Home-Sweet-Home-Assistant/Comms-Badge-Voice-Assistant/Hardware/KiCad Project/v0.1.1/Antenna.kicad_sch

## KiCad design Hardware/KiCad Project/v0.1.1/Antenna.kicad_sch (2024-03-10)

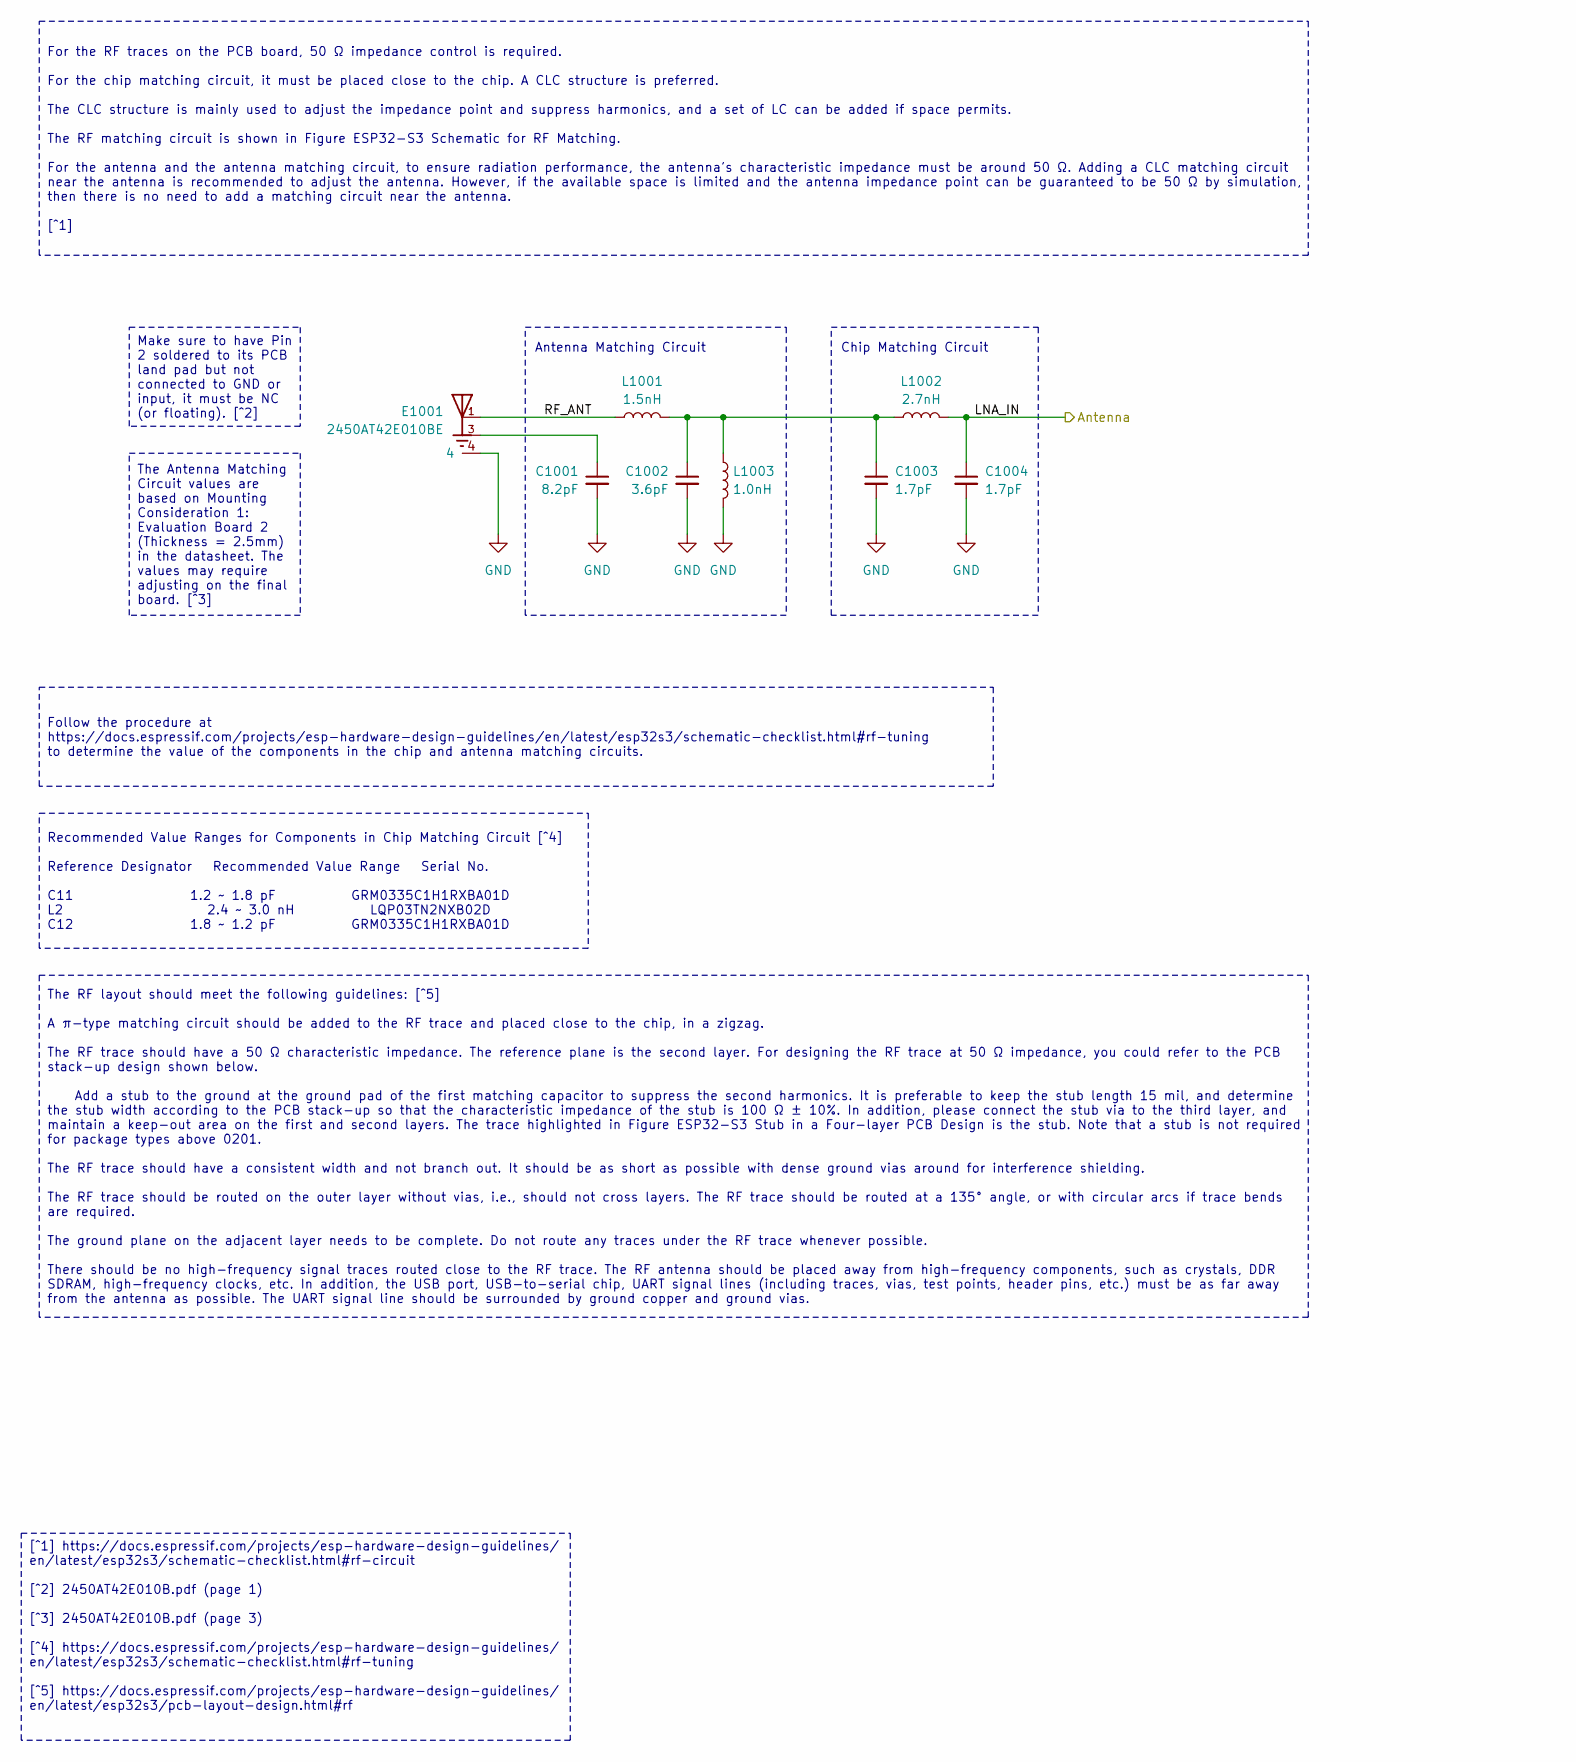
[picture p19: schematic Antenna.kicad_sch]

Parts:
C1001: 8.2pF; C_0402_1005Metric; Mfr. Part # GRM1555C1H8R2CA01D; LCSC # C76984
C1002: 3.6pF; C_0402_1005Metric; Mfr. Part # GRM1555C1H3R6CA01D; LCSC # C913745
C1003, C1004: 1.7pF; C_0402_1005Metric; Mfr. Part # GJM1555C1H1R7BB01D; LCSC # C161313
E1001: 2450AT42E010BE; XDCR_2450AT42E010BE; Mfr. Part # 2450AT42E010B001E; LCSC # C17243480
L1001: 1.5nH; L_0402_1005Metric_Pad0.77x0.64mm_HandSolder; Mfr. Part # LQG15HN1N5B02D; LCSC # C3911113
L1002: 2.7nH; L_0402_1005Metric_Pad0.77x0.64mm_HandSolder; Mfr. Part # LQG15HS2N7B02D; LCSC # C162541
L1003: 1.0nH; L_0402_1005Metric_Pad0.77x0.64mm_HandSolder; Mfr. Part # LQG15HS1N0B02D; LCSC # C162538

Connections:
Antenna: C1004.1, L1002.2
GND: C1001.2, C1002.2, C1003.2, C1004.2, E1001.4, L1003.2
unnamed: C1001.1, E1001.3
unnamed: C1002.1, C1003.1, L1001.2, L1002.1, L1003.1
RF_ANT: E1001.1, L1001.1

Notes on the sheet:
The RF layout should meet the following guidelines: [^5] A π-type matching circuit should be added to the RF trace and placed close to the chip, in a zigzag. The RF trace should have a 50 Ω characteristic impedance. The reference plane is the second layer. For designing the RF trace at 50 Ω impedan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
Recommended Value Ranges for Components in Chip Matching Circuit [^4] Reference Designator Recommended Value Range Serial No. C11 1.2 ~ 1.8 pF GRM0335C1H1RXBA01D L2 2.4 ~ 3.0 nH LQP03TN2NXB02D C12 1.8 ~ 1.2 pF GRM0335C1H1RXBA01D
Follow the procedure at https://docs.espressif.com/projects/esp-hardware-design-guidelines/en/latest/esp32s3/schematic-checklist.html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 to determine the value of the components in the chip and antenna matching circuits.
Make sure to have Pin 2 soldered to its PCB land pad but not connected to GND or input, it must be NC (or floating). [^2]
[^1] https://docs.espressif.com/projects/esp-hardware-design-guidelines/ en/latest/esp32s3/schematic-checklist.html#rf-circuit [^2] 2450AT42E010B.pdf (page 1) [^3] 2450AT42E010B.pdf (page 3) [^4] https://docs.espressif.com/projects/esp-hardware-design-guidelines/ en/latest/esp32s3/schematic-checkli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
The Antenna Matching Circuit values are based on Mounting Consideration 1: Evaluation Board 2 (Thickness = 2.5mm) in the datasheet. The values may require adjusting on the final board. [^3]
For the RF traces on the PCB board, 50 Ω impedance control is required. For the chip matching circuit, it must be placed close to the chip. A CLC structure is preferred. The CLC structure is mainly used to adjust the impedance point and suppress harmonics, and a set of LC can be added if space perm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
Chip Matching Circuit
Antenna Matching Circuit
