Home-Sweet-Home-Assistant/Comms-Badge-Voice-Assistant/Hardware/KiCad Project/v0.1.1/Charging_Battery_Protection.kicad_sch

## KiCad design Hardware/KiCad Project/v0.1.1/Charging_Battery_Protection.kicad_sch (2024-03-10)

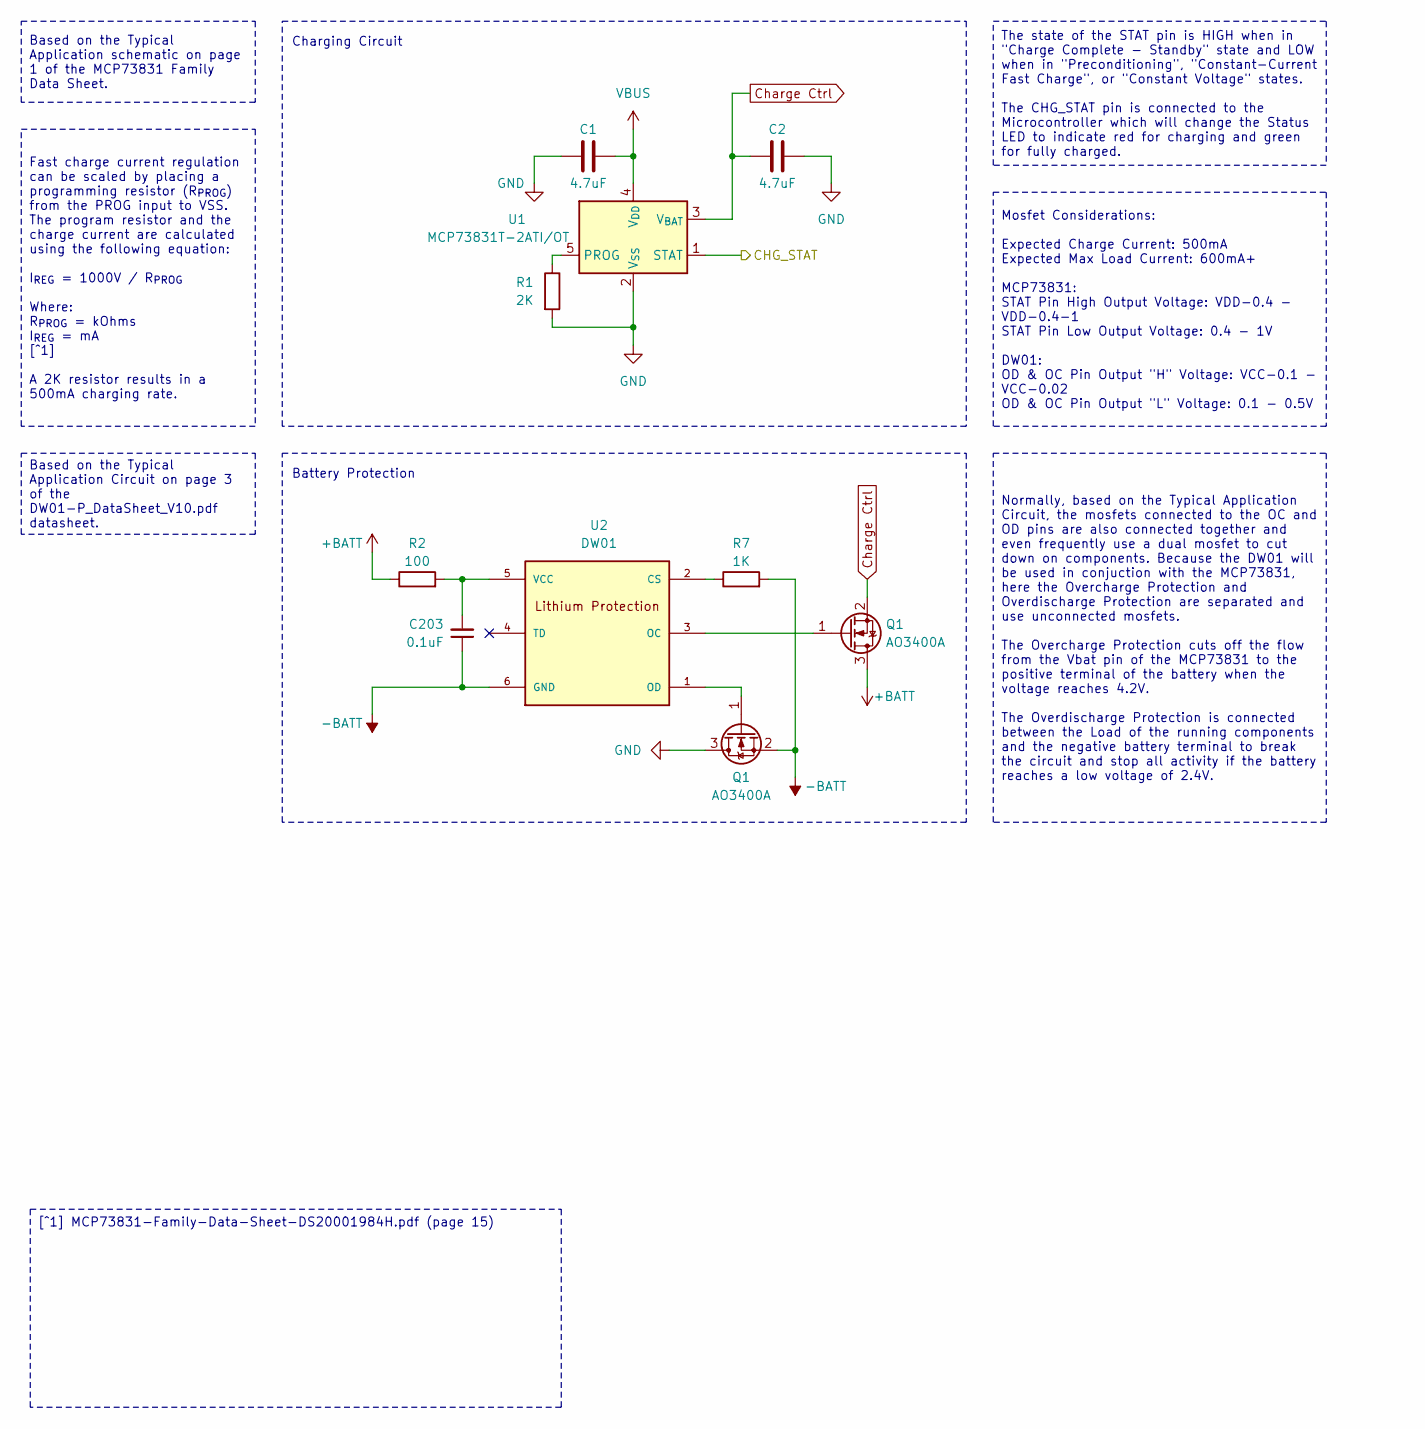
[picture p20: schematic Charging_Battery_Protection.kicad_sch]

Parts:
C1, C2: 4.7uF; C_0402_1005Metric; Mfr. Part # GRM155R61A475KEAAD; LCSC # C77004
C203: 0.1uF; C_0402_1005Metric; Mfr. Part # GRM155R61H104JE14D; LCSC # C426067
Q1: AO3400A; SOT-23; Mfr. Part # AO3400A; LCSC # C20917
R1: 2K; R_0402_1005Metric; Mfr. Part # RC0402FR-072KL; LCSC # C60488
R2: 100; R_0402_1005Metric; Mfr. Part # RC0402FR-07100RL; LCSC # C106232
R7: 1K; R_0402_1005Metric; Mfr. Part # RC0402FR-071KL; LCSC # C106235
U1: MCP73831T-2ATI/OT; SOT-23-5; Mfr. Part # MCP73831T-2ATI/OT; LCSC # C14879
U2: DW01; SOT23-6; Mfr. Part # DW01; LCSC # C686633

Connections:
+BATT: Q1.3 (D), R2.1
-BATT: C203.1, Q1.2 (S), R7.2, U2.6 (GND)
CHG_STAT: U1.1 (STAT)
Charge Ctrl: C2.2, Q1.2 (S), U1.3 (V_{BAT})
GND: C1.2, C2.1, Q1.3 (D), R1.2, U1.2 (V_{SS})
unnamed: C203.2, R2.2, U2.5 (VCC)
unnamed: Q1.1 (G), U2.1 (OD), U2.3 (OC)
unnamed: R1.1, U1.5 (PROG)
unnamed: R7.1, U2.2 (CS)
VBUS: C1.1, U1.4 (V_{DD})

Notes on the sheet:
Fast charge current regulation can be scaled by placing a programming resistor (R_{PROG}) from the PROG input to VSS. The program resistor and the charge current are calculated using the following equation: I_{REG} = 1000V / R_{PROG} Where: R_{PROG} = kOhms I_{REG} = mA [^1] A 2K resistor results i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
Normally, based on the Typical Application Circuit, the mosfets connected to the OC and OD pins are also connected together and even frequently use a dual mosfet to cut down on components. Because the DW01 will be used in conjuction with the MCP73831, here the Overcharge Protection and Overdischarg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
Based on the Typical Application Circuit on page 3 of the DW01-P_DataSheet_V10.pdf datasheet.
The state of the STAT pin is HIGH when in "Charge Complete - Standby" state and LOW when in "Preconditioning", "Constant-Current Fast Charge", or "Constant Voltage" states. The CHG_STAT pin is connected to the Microcontroller which will change the Status LED to indicate red for charging and green f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
[^1] MCP73831-Family-Data-Sheet-DS20001984H.pdf (page 15)
Based on the Typical Application schematic on page 1 of the MCP73831 Family Data Sheet.
Mosfet Considerations: Expected Charge Current: 500mA Expected Max Load Current: 600mA+ MCP73831: STAT Pin High Output Voltage: VDD-0.4 - VDD-0.4-1 STAT Pin Low Output Voltage: 0.4 - 1V DW01: OD & OC Pin Output "H" Voltage: VCC-0.1 - VCC-0.02 OD & OC Pin Output "L" Voltage: 0.1 - 0.5V
Charging Circuit
Battery Protection
