Home-Sweet-Home-Assistant/Comms-Badge-Voice-Assistant/Hardware/KiCad Project/v0.1.1/Clock_Source.kicad_sch

## KiCad design Hardware/KiCad Project/v0.1.1/Clock_Source.kicad_sch (2024-03-10)

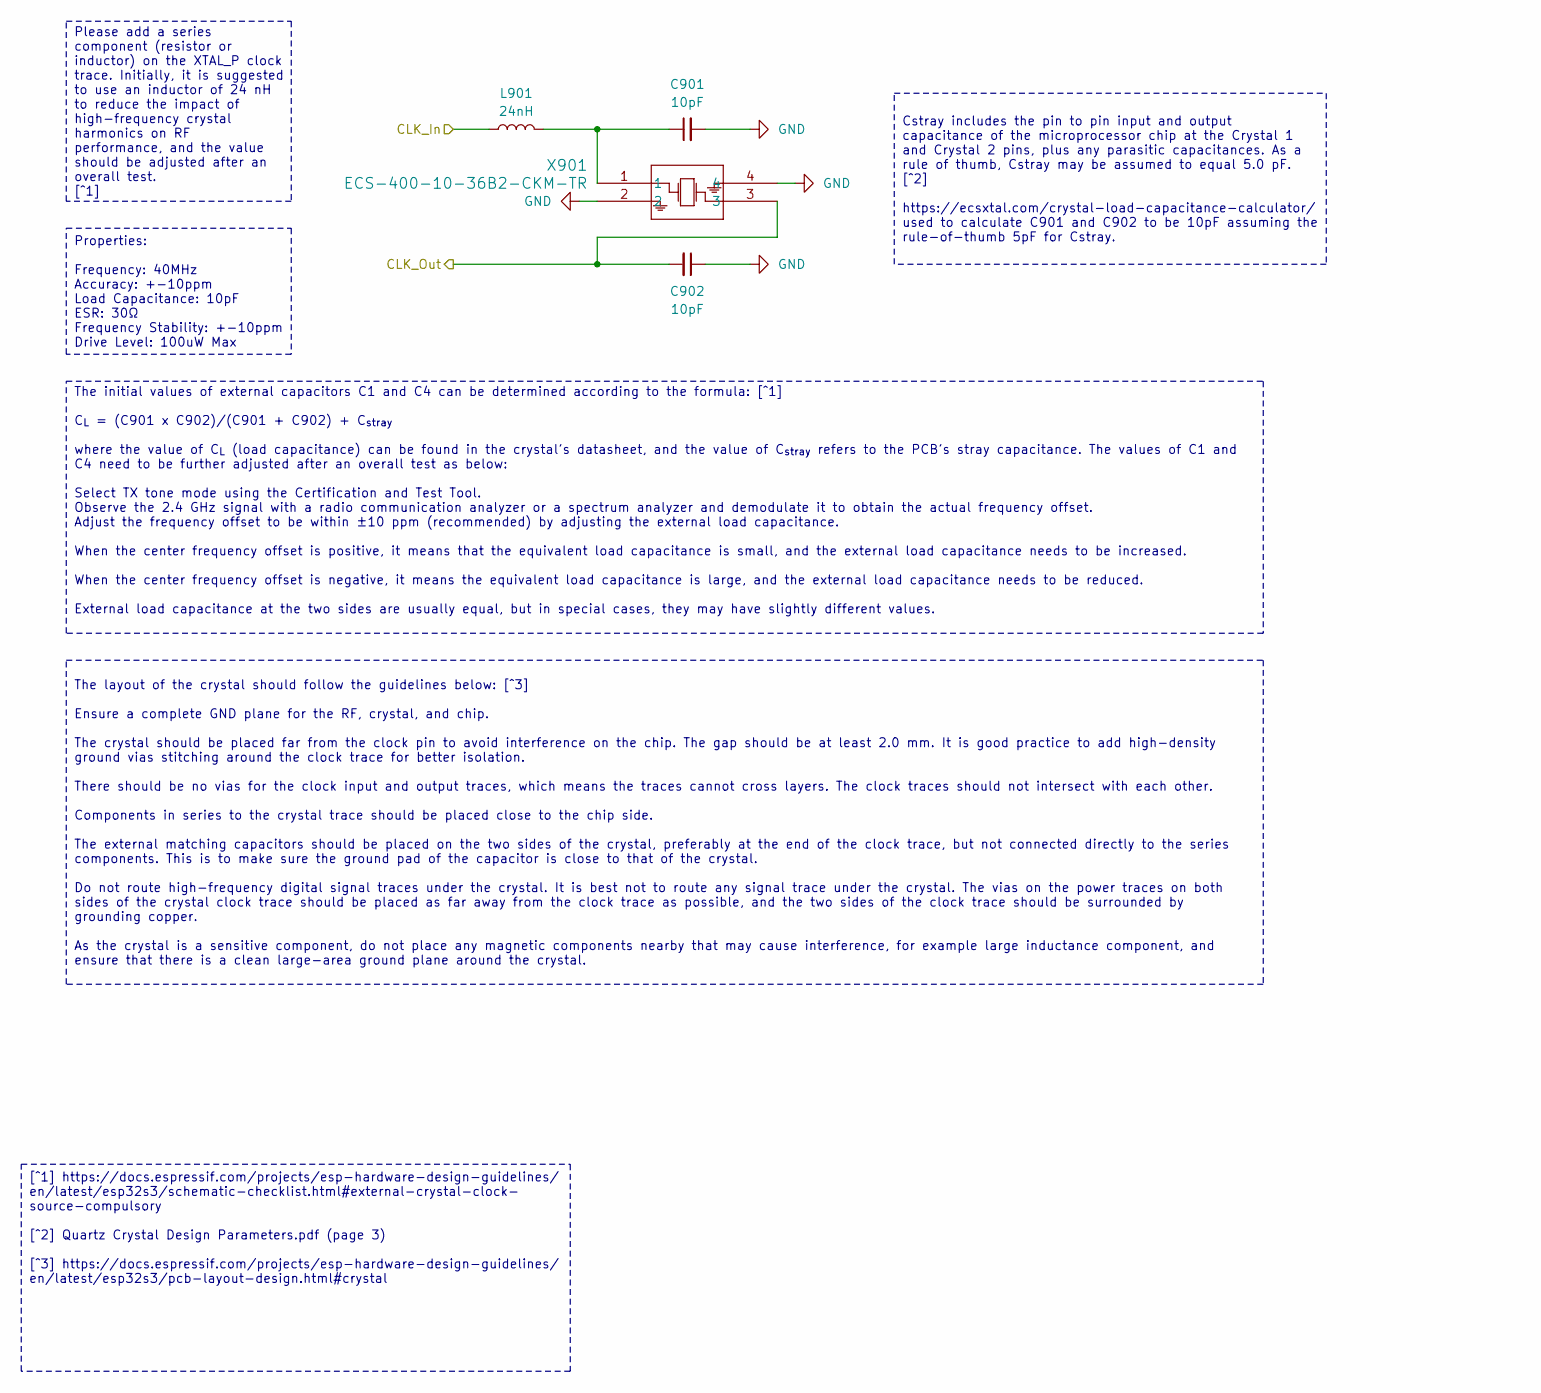
[picture p21: schematic Clock_Source.kicad_sch]

Parts:
C901, C902: 10pF; C_0402_1005Metric; Mfr. Part # GRM1555C1H100JA01D; LCSC # C76946
L901: 24nH; L_0402_1005Metric_Pad0.77x0.64mm_HandSolder; Mfr. Part # FHW0402UC024JST; LCSC # C317961
X901: ECS-400-10-36B2-CKM-TR; ECS-400_ECS; Mfr. Part # ECS-400-10-36B2-CKM-TR; LCSC # NA

Connections:
CLK_In: L901.1
CLK_Out: C902.2, X901.3
GND: C901.2, C902.1, X901.2, X901.4
unnamed: C901.1, L901.2, X901.1

Notes on the sheet:
Cstray includes the pin to pin input and output capacitance of the microprocessor chip at the Crystal 1 and Crystal 2 pins, plus any parasitic capacitances. As a rule of thumb, Cstray may be assumed to equal 5.0 pF. [^2] https://ecsxtal.com/crystal-load-capacitance-calculator/ used to calculate C90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
The layout of the crystal should follow the guidelines below: [^3] Ensure a complete GND plane for the RF, crystal, and chip. The crystal should be placed far from the clock pin to avoid interference on the chip. The gap should be at least 2.0 mm. It is good practice to add high-density ground vias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
Properties: Frequency: 40MHz Accuracy: +-10ppm Load Capacitance: 10pF ESR: 30Ω Frequency Stability: +-10ppm Drive Level: 100uW Max
[^1] https://docs.espressif.com/projects/esp-hardware-design-guidelines/ en/latest/esp32s3/schematic-checklist.html#external-crystal-clock- source-compulsory [^2] Quartz Crystal Design Parameters.pdf (page 3) [^3] https://docs.espressif.com/projects/esp-hardware-design-guidelines/ en/latest/esp32s3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
The initial values of external capacitors C1 and C4 can be determined according to the formula: [^1] C_{L} = (C901 x C902)/(C901 + C902) + C_{stray} where the value of C_{L} (load capacitance) can be found in the crystal's datasheet, and the value of C_{stray} refers to the PCB's stray capacitance.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
Please add a series component (resistor or inductor) on the XTAL_P clock trace. Initially, it is suggested to use an inductor of 24 nH to reduce the impact of high-frequency crystal harmonics on RF performance, and the value should be adjusted after an overall test. [^1]
