Home-Sweet-Home-Assistant/Comms-Badge-Voice-Assistant/Hardware/KiCad Project/v0.1.1/Flash_PSRAM.kicad_sch

## KiCad design Hardware/KiCad Project/v0.1.1/Flash_PSRAM.kicad_sch (2024-03-10)

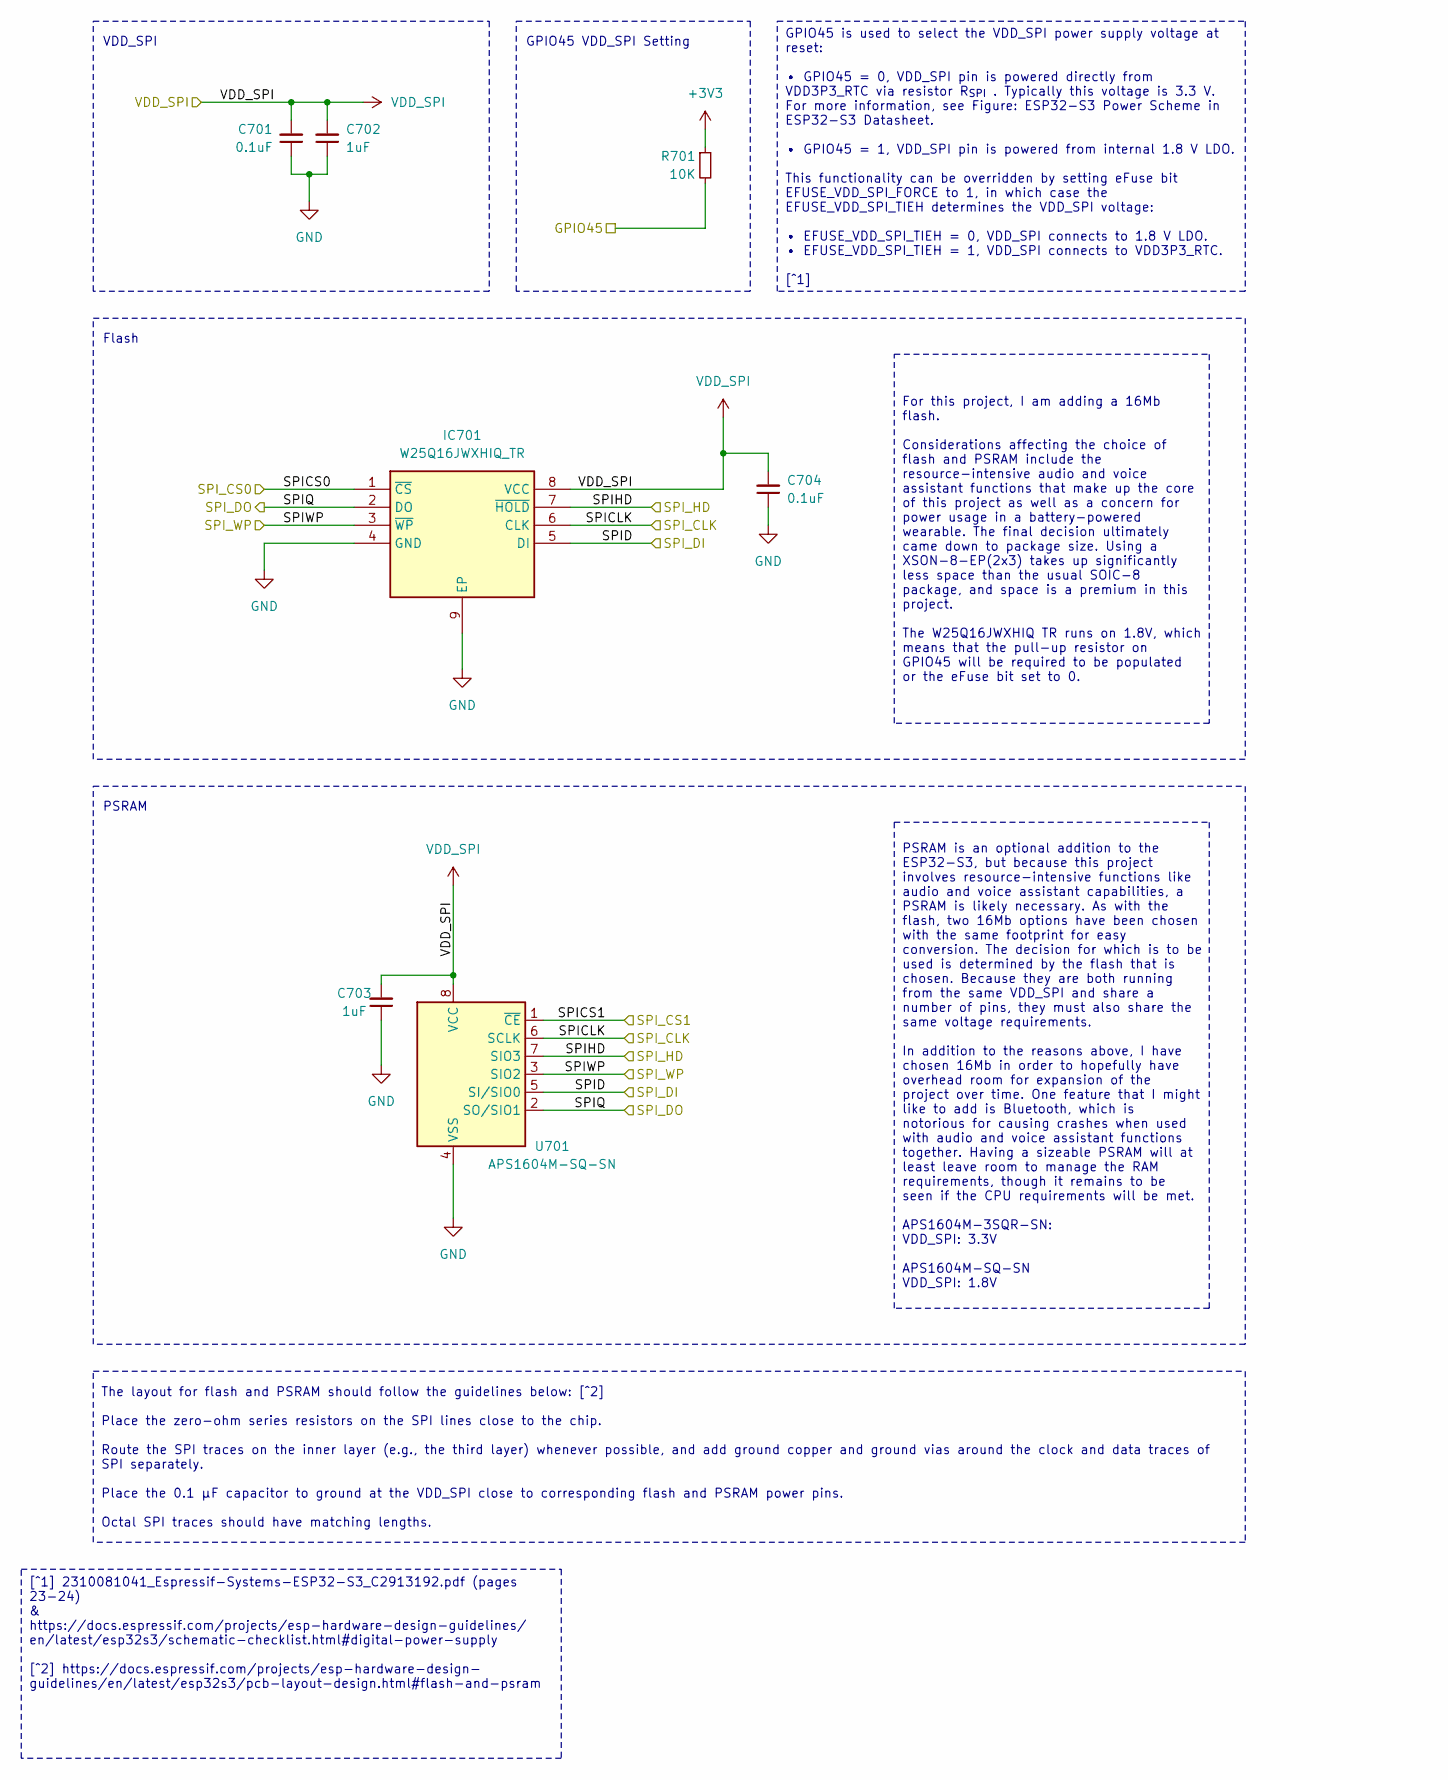
[picture p22: schematic Flash_PSRAM.kicad_sch]

Parts:
C701, C704: 0.1uF; C_0402_1005Metric; Mfr. Part # GRM155R61H104JE14D; LCSC # C426067
C702, C703: 1uF; C_0402_1005Metric; Mfr. Part # GRM155R61E105KA12D; LCSC # C77009
IC701: W25Q16JWXHIQ_TR; SON50P300X200X40-9N; Mfr. Part # W25Q16JWXHIQ TR; LCSC # C2835333
R701: 10K; R_0402_1005Metric; Mfr. Part # RC0402FR-0710KL; DigiKey # 311-10.0KLRCT-ND
U701: APS1604M-SQ-SN; SOIC-8_3.9x4.9mm_P1.27mm; Mfr. Part # APS1604M-SQ-SN; LCSC # NA

Connections:
+3V3: R701.1
GND: C701.1, C702.1, C703.1, C704.1, IC701.4 (GND), IC701.9 (EP), U701.4 (VSS)
GPIO45: R701.2
SPI_CLK: IC701.6 (CLK), U701.6 (SCLK)
SPI_CS0: IC701.1 (~CS)
SPI_CS1: U701.1 (~CE)
SPI_DI: IC701.5 (DI), U701.5 (SI/SIO0)
SPI_DO: IC701.2 (DO), U701.2 (SO/SIO1)
SPI_HD: IC701.7 (~HOLD), U701.7 (SIO3)
SPI_WP: IC701.3 (~WP), U701.3 (SIO2)
VDD_SPI: C701.2, C702.2, C703.2, C704.2, IC701.8 (VCC), U701.8 (VCC)

Notes on the sheet:
[^1] 2310081041_Espressif-Systems-ESP32-S3_C2913192.pdf (pages 23-24) & https://docs.espressif.com/projects/esp-hardware-design-guidelines/ en/latest/esp32s3/schematic-checklist.html#digital-power-supply [^2] https://docs.espressif.com/projects/esp-hardware-design- guidelines/en/latest/esp32s3/pcb-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
For this project, I am adding a 16Mb flash. Considerations affecting the choice of flash and PSRAM include the resource-intensive audio and voice assistant functions that make up the core of this project as well as a concern for power usage in a battery-powered wearable. The final decision ultimate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
GPIO45 is used to select the VDD_SPI power supply voltage at reset: • GPIO45 = 0, VDD_SPI pin is powered directly from VDD3P3_RTC via resistor R_{SPI} . Typically this voltage is 3.3 V. For more information, see Figure: ESP32-S3 Power Scheme in ESP32-S3 Datasheet. • GPIO45 = 1, VDD_SPI pin is power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
PSRAM is an optional addition to the ESP32-S3, but because this project involves resource-intensive functions like audio and voice assistant capabilities, a PSRAM is likely necessary. As with the flash, two 16Mb options have been chosen with the same footprint for easy conversion. The decision for 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
The layout for flash and PSRAM should follow the guidelines below: [^2] Place the zero-ohm series resistors on the SPI lines close to the chip. Route the SPI traces on the inner layer (e.g., the third layer) whenever possible, and add ground copper and ground vias around the clock and data traces o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
VDD_SPI
PSRAM
GPIO45 VDD_SPI Setting
Flash
