Home-Sweet-Home-Assistant/Comms-Badge-Voice-Assistant/Hardware/KiCad Project/v0.1.1/Microcontroller.kicad_sch

## KiCad design Hardware/KiCad Project/v0.1.1/Microcontroller.kicad_sch (2024-03-10)

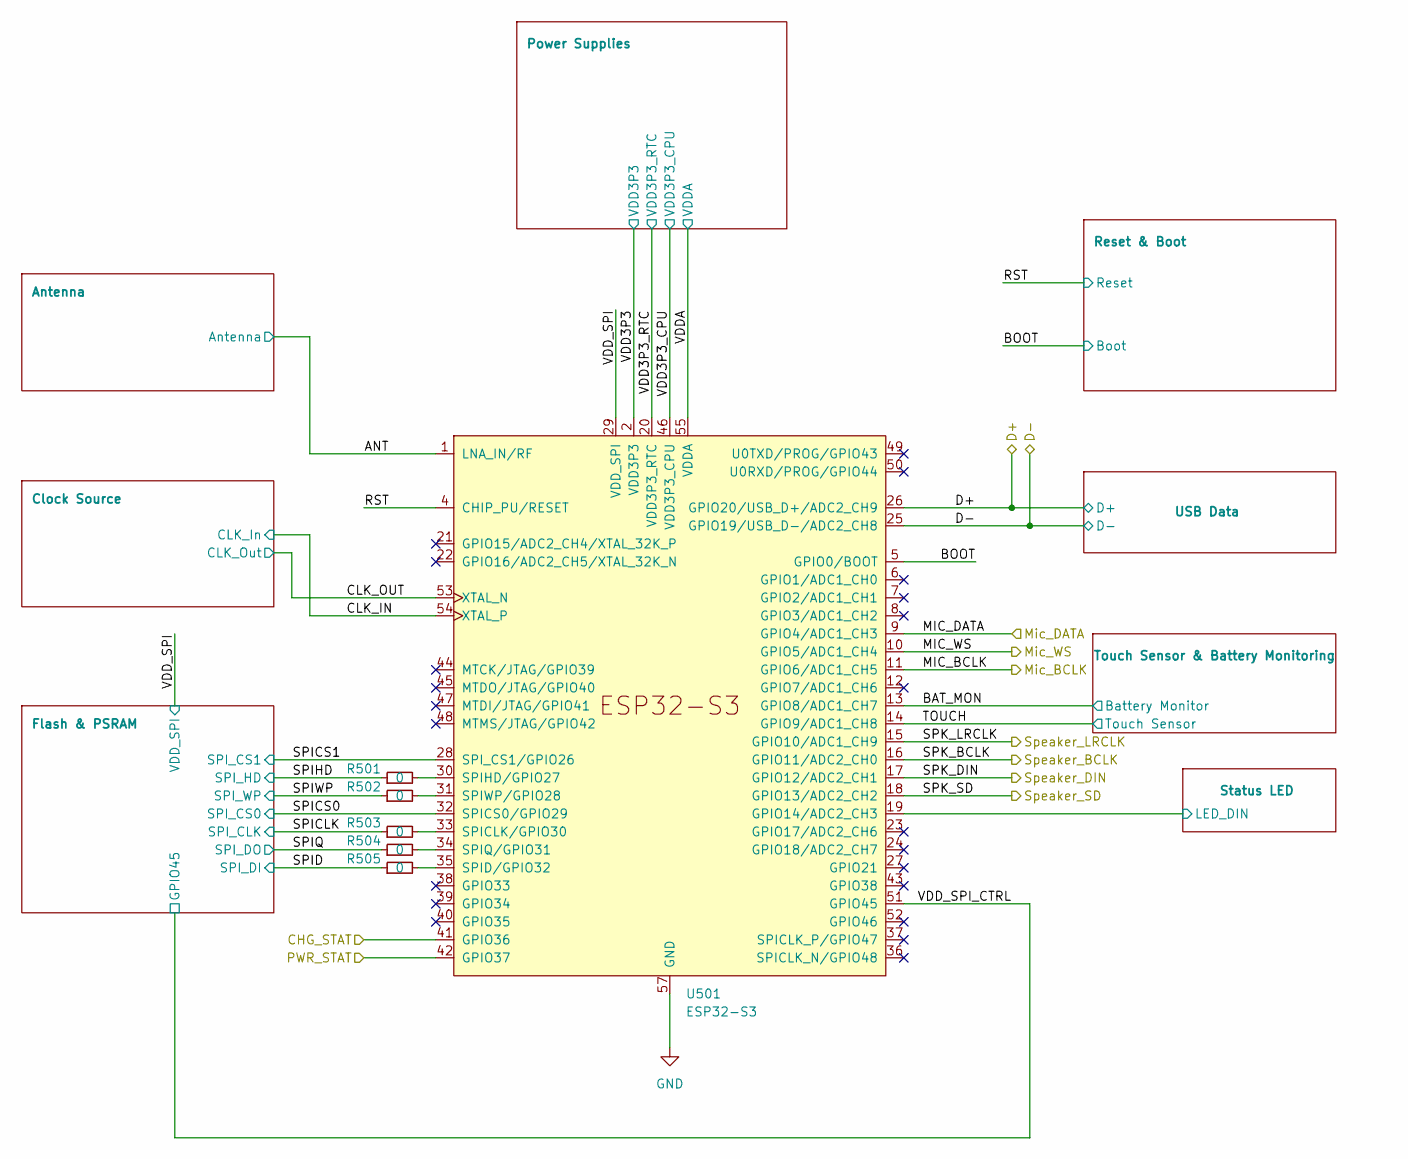
[picture p23: schematic Microcontroller.kicad_sch]

Parts:
R501: 0; R_0402_1005Metric; Mfr. Part # RC0402FR-070RL; LCSC # C106231
R502, R503, R504, R505: 0; R_0402_1005Metric; Mfr. Part # RC0402FR-070RL; DigiKey # 311-0.0LRCT-ND
U501: ESP32-S3; QFN-56-1EP_7x7mm_P0.4mm_EP5.6x5.6mm; Mfr. Part # ESP32-S3; LCSC # C2913192

Connections:
ANT: U501.1 (LNA_IN/RF)
BAT_MON: U501.13 (GPIO8/ADC1_CH7)
BOOT: U501.5 (GPIO0/BOOT)
CHG_STAT: U501.41 (GPIO36)
CLK_IN: U501.54 (XTAL_P)
CLK_OUT: U501.53 (XTAL_N)
D+: U501.26 (GPIO20/USB_D+/ADC2_CH9)
D-: U501.25 (GPIO19/USB_D-/ADC2_CH8)
GND: U501.57 (GND)
LED_DIN: U501.19 (GPIO14/ADC2_CH3)
Mic_BCLK: U501.11 (GPIO6/ADC1_CH5)
Mic_DATA: U501.9 (GPIO4/ADC1_CH3)
Mic_WS: U501.10 (GPIO5/ADC1_CH4)
unnamed: R501.2, U501.30 (SPIHD/GPIO27)
unnamed: R502.2, U501.31 (SPIWP/GPIO28)
unnamed: R503.2, U501.33 (SPICLK/GPIO30)
unnamed: R504.2, U501.34 (SPIQ/GPIO31)
unnamed: R505.2, U501.35 (SPID/GPIO32)
PWR_STAT: U501.42 (GPIO37)
RST: U501.4 (CHIP_PU/RESET)
SPICLK: R503.1
SPICS0: U501.32 (SPICS0/GPIO29)
SPICS1: U501.28 (SPI_CS1/GPIO26)
SPID: R505.1
SPIHD: R501.1
SPIQ: R504.1
SPIWP: R502.1
Speaker_BCLK: U501.16 (GPIO11/ADC2_CH0)
Speaker_DIN: U501.17 (GPIO12/ADC2_CH1)
Speaker_LRCLK: U501.15 (GPIO10/ADC1_CH9)
Speaker_SD: U501.18 (GPIO13/ADC2_CH2)
TOUCH: U501.14 (GPIO9/ADC1_CH8)
VDD3P3: U501.2 (VDD3P3), U501.3 (VDD3P3)
VDD3P3_CPU: U501.46 (VDD3P3_CPU)
VDD3P3_RTC: U501.20 (VDD3P3_RTC)
VDDA: U501.55 (VDDA), U501.56 (VDDA)
VDD_SPI: U501.29 (VDD_SPI)
VDD_SPI_CTRL: U501.51 (GPIO45)
