Home-Sweet-Home-Assistant/Comms-Badge-Voice-Assistant/Hardware/KiCad Project/v0.1.1/Microcontroller_Power_Supplies.kicad_sch

## KiCad design Hardware/KiCad Project/v0.1.1/Microcontroller_Power_Supplies.kicad_sch (2024-03-10)

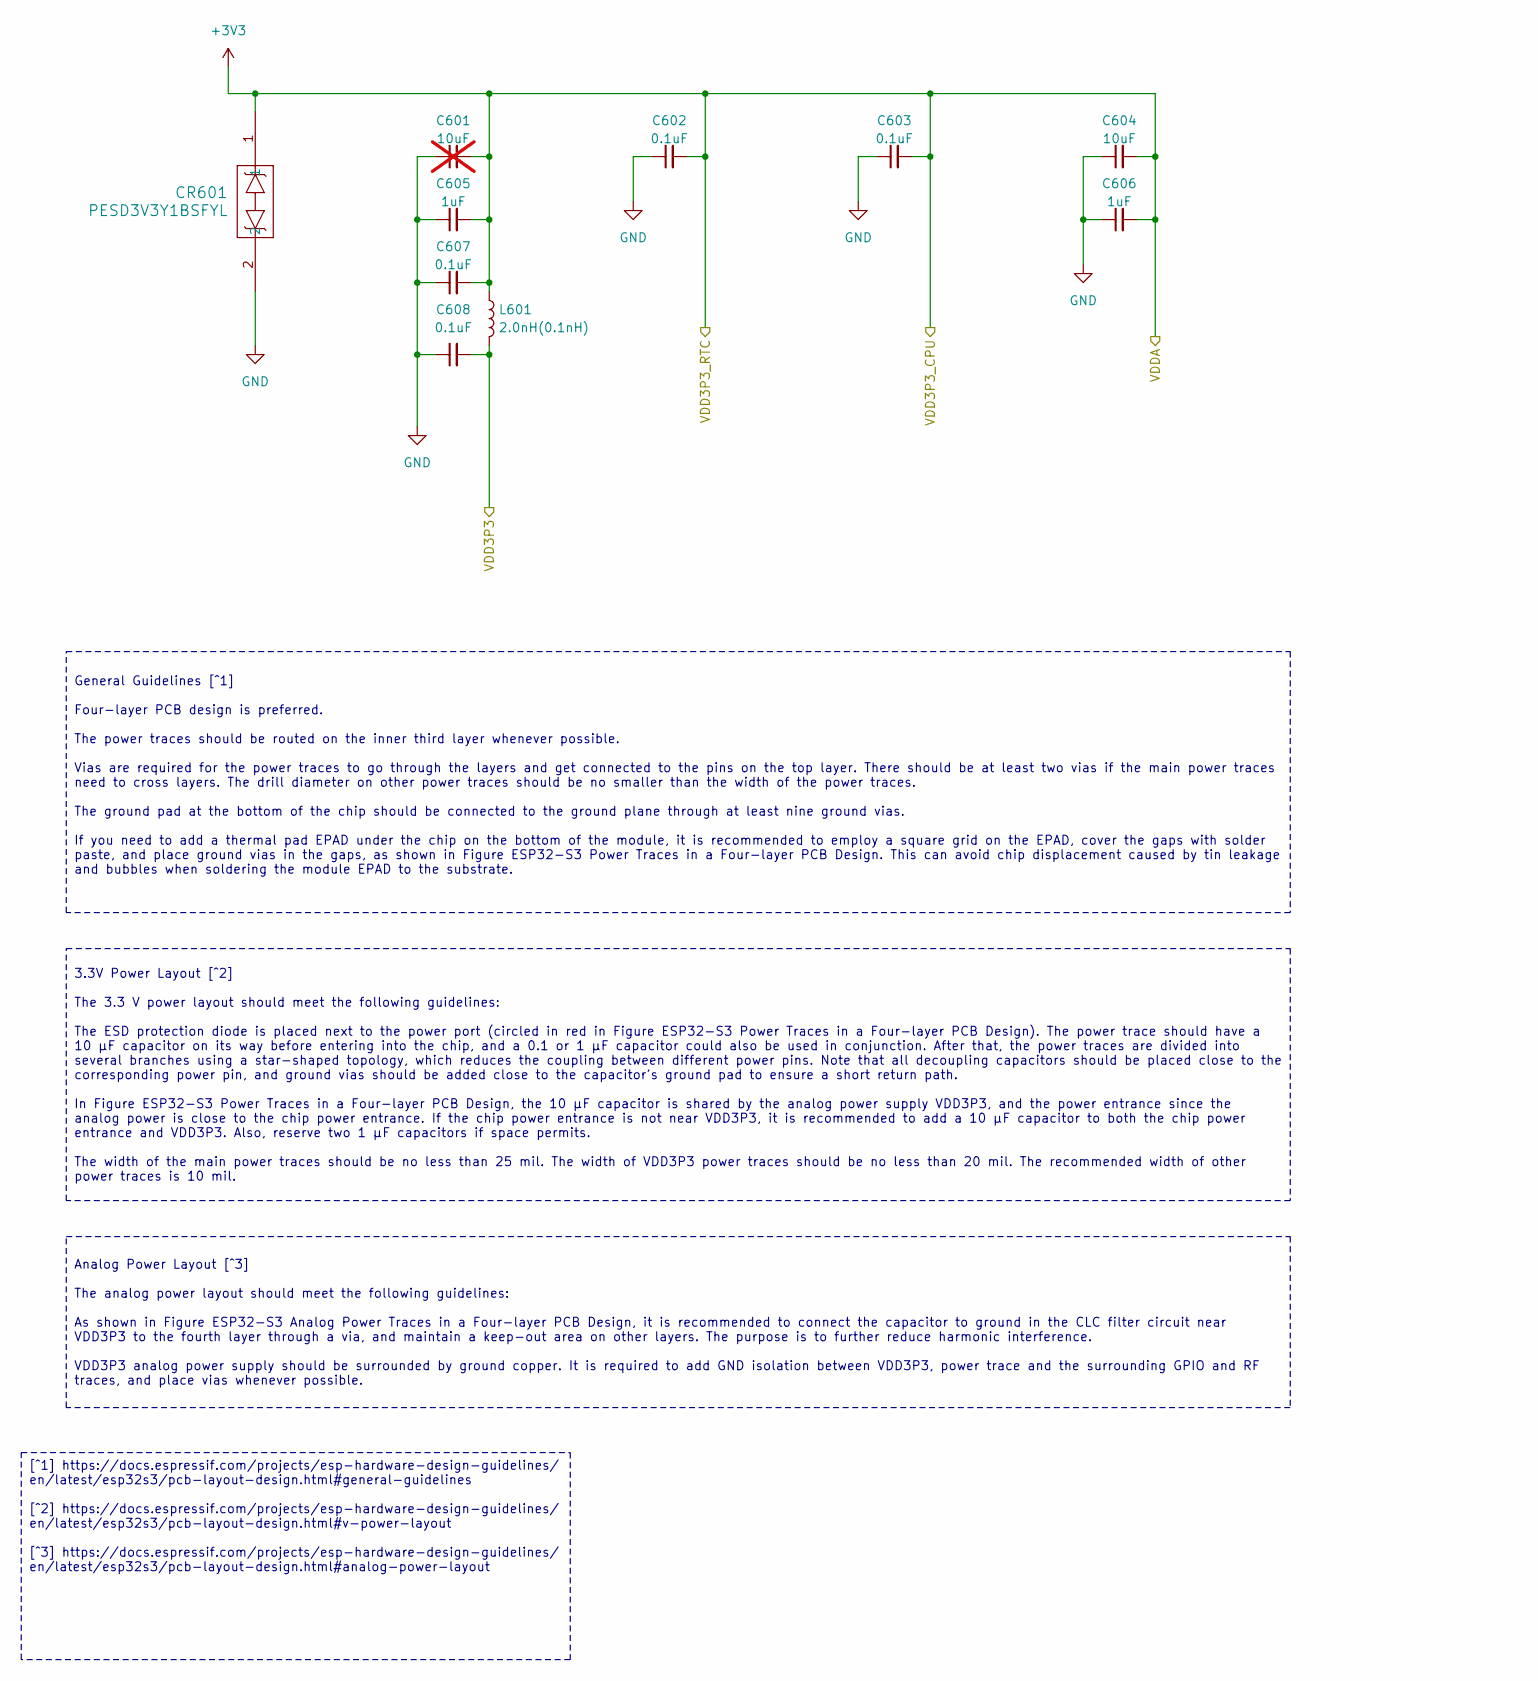
[picture p24: schematic Microcontroller_Power_Supplies.kicad_sch]

Parts:
C601: 10uF; C_0402_1005Metric; Mfr. Part # GRM155R61A106ME11D; LCSC # C408132; not fitted
C602, C603, C607, C608: 0.1uF; C_0402_1005Metric; Mfr. Part # GRM155R61H104JE14D; LCSC # C426067
C604: 10uF; C_0402_1005Metric; Mfr. Part # GRM155R61A106ME11D; LCSC # C408132
C605, C606: 1uF; C_0402_1005Metric; Mfr. Part # GRM155R61E105KA12D; LCSC # C77009
CR601: PESD3V3Y1BSFYL; SOD962-2_DSN0603-2_NEX; Mfr. Part # PESD4V0Y1BSFYL; LCSC # C552545
L601: 2.0nH(0.1nH); L_0402_1005Metric_Pad0.77x0.64mm_HandSolder; Mfr. Part # LQG15HS2N0B02D; LCSC # C2986275

Connections:
+3V3: C601.2, C602.2, C603.2, C604.2, C605.2, C606.2, C607.2, CR601.1, L601.1
GND: C601.1, C602.1, C603.1, C604.1, C605.1, C606.1, C607.1, C608.1, CR601.2
VDD3P3: C608.2, L601.2

Notes on the sheet:
Analog Power Layout [^3] The analog power layout should meet the following guidelines: As shown in Figure ESP32-S3 Analog Power Traces in a Four-layer PCB Design, it is recommended to connect the capacitor to ground in the CLC filter circuit near VDD3P3 to the fourth layer through a via, and mainta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
[^1] https://docs.espressif.com/projects/esp-hardware-design-guidelines/ en/latest/esp32s3/pcb-layout-design.html#general-guidelines [^2] https://docs.espressif.com/projects/esp-hardware-design-guidelines/ en/latest/esp32s3/pcb-layout-design.html#v-power-layout [^3] https://docs.espressif.com/proje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
3.3V Power Layout [^2] The 3.3 V power layout should meet the following guidelines: The ESD protection diode is placed next to the power port (circled in red in Figure ESP32-S3 Power Traces in a Four-layer PCB Design). The power trace should have a 10 µF capacitor on its way before entering into th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
General Guidelines [^1] Four-layer PCB design is preferred. The power traces should be routed on the inner third layer whenever possible. Vias are required for the power traces to go through the layers and get connected to the pins on the top layer. There should be at least two vias if the main pow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
