Home-Sweet-Home-Assistant/Comms-Badge-Voice-Assistant/Hardware/KiCad Project/v0.1.1/Reset_Boot.kicad_sch

## KiCad design Hardware/KiCad Project/v0.1.1/Reset_Boot.kicad_sch (2024-03-10)

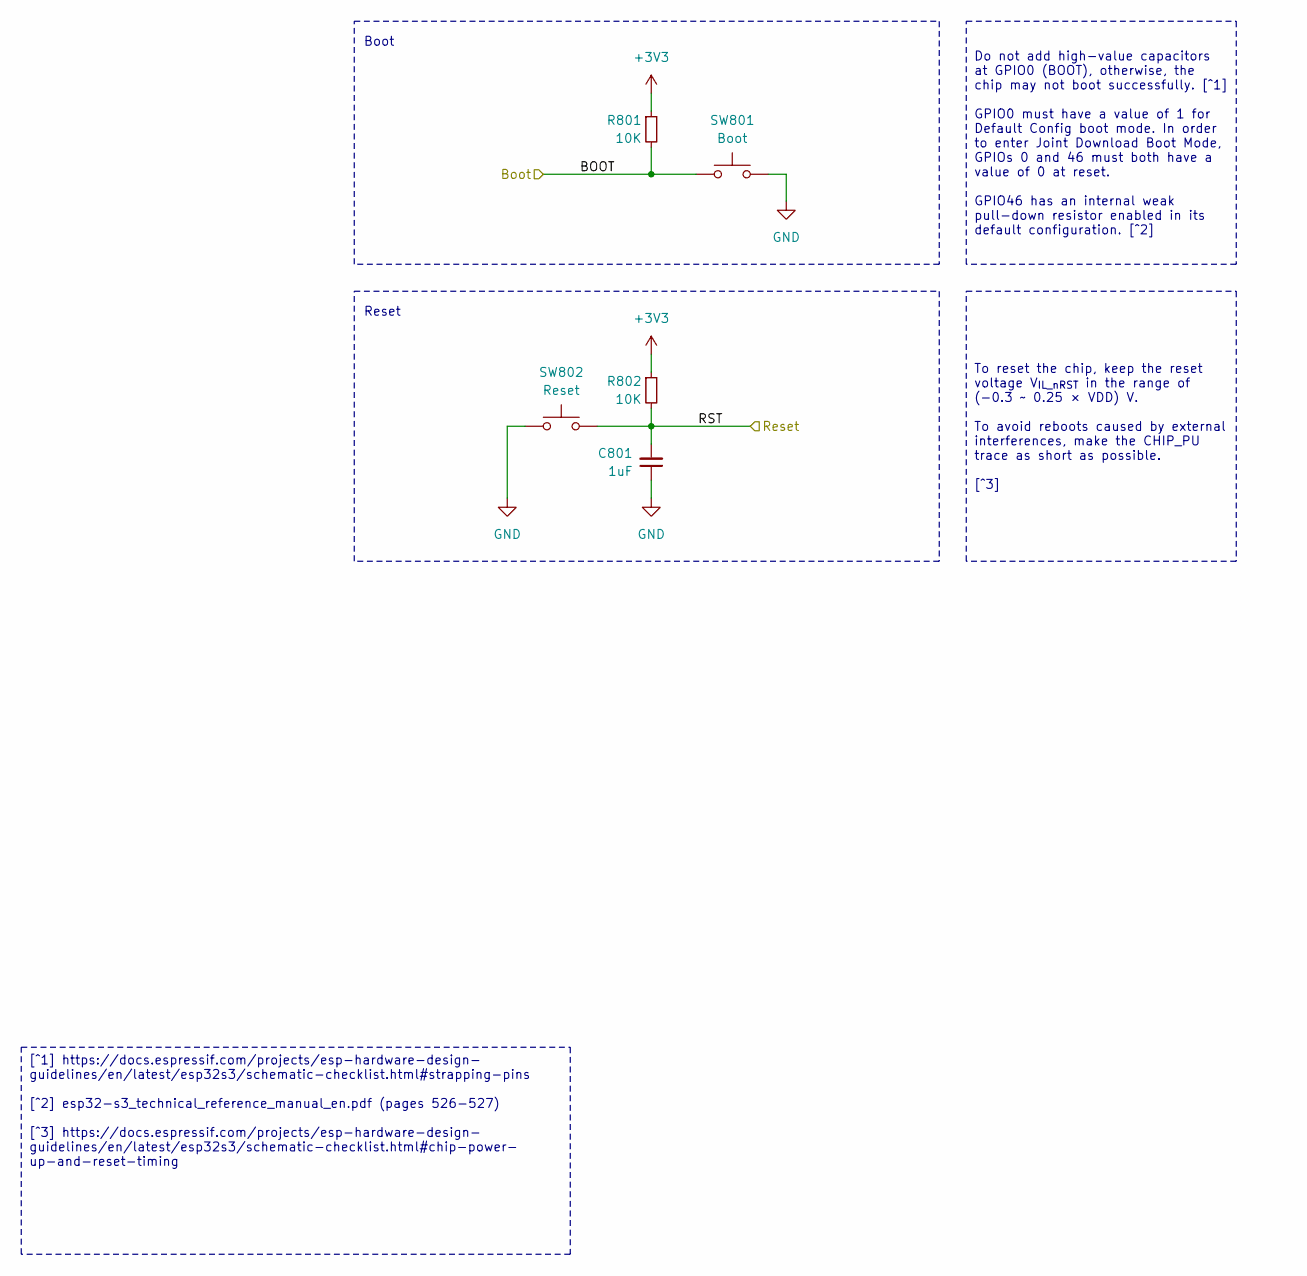
[picture p25: schematic Reset_Boot.kicad_sch]

Parts:
C801: 1uF; C_0402_1005Metric; Mfr. Part # GRM155R61E105KA12D; LCSC # C77009
R801, R802: 10K; R_0402_1005Metric; Mfr. Part # RC0402FR-0710KL; DigiKey # 311-10.0KLRCT-ND
SW801: Boot; SW_Push_SPST_NO_Alps_SKRK; Mfr. Part # XDTD-0304-215; LCSC # C7498203
SW802: Reset; SW_Push_SPST_NO_Alps_SKRK; Mfr. Part # XDTD-0304-215; LCSC # C7498203

Connections:
+3V3: R801.1, R802.1
Boot: R801.2, SW801.1
GND: C801.1, SW801.2, SW802.1
Reset: C801.2, R802.2, SW802.2

Notes on the sheet:
[^1] https://docs.espressif.com/projects/esp-hardware-design- guidelines/en/latest/esp32s3/schematic-checklist.html#strapping-pins [^2] esp32-s3_technical_reference_manual_en.pdf (pages 526-527) [^3] https://docs.espressif.com/projects/esp-hardware-design- guidelines/en/latest/esp32s3/schematic-che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
Do not add high-value capacitors at GPIO0 (BOOT), otherwise, the chip may not boot successfully. [^1] GPIO0 must have a value of 1 for Default Config boot mode. In order to enter Joint Download Boot Mode, GPIOs 0 and 46 must both have a value of 0 at reset. GPIO46 has an internal weak pull-down res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
To reset the chip, keep the reset voltage V_{IL_nRST} in the range of (-0.3 ~ 0.25 × VDD) V. To avoid reboots caused by external interferences, make the CHIP_PU trace as short as possible. [^3]
Reset
Boot
