Home-Sweet-Home-Assistant/Comms-Badge-Voice-Assistant/Hardware/KiCad Project/v0.1.1/Speaker_Microphone.kicad_sch

## KiCad design Hardware/KiCad Project/v0.1.1/Speaker_Microphone.kicad_sch (2024-03-10)

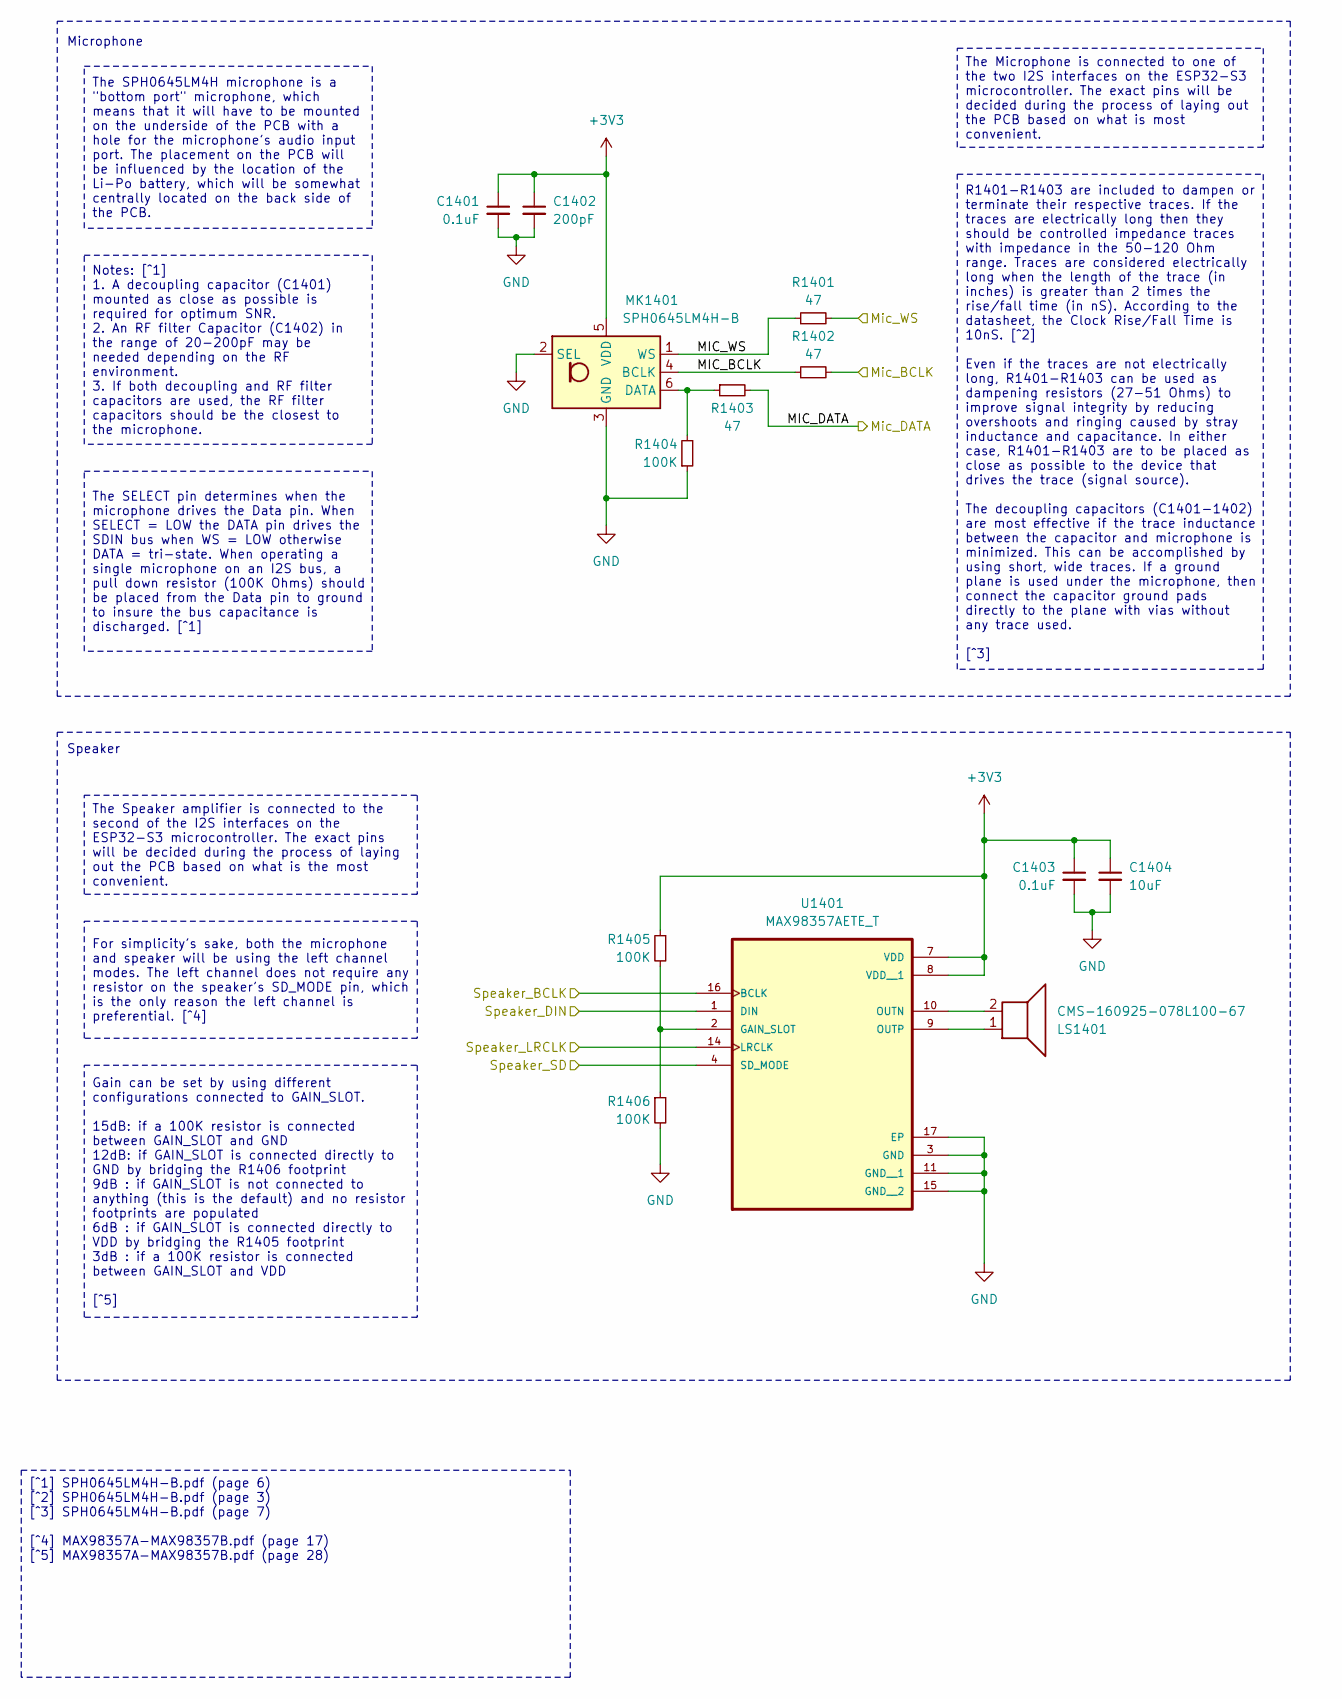
[picture p26: schematic Speaker_Microphone.kicad_sch]

Parts:
C1401, C1403: 0.1uF; C_0402_1005Metric; Mfr. Part # GRM155R61H104JE14D; LCSC # C426067
C1402: 200pF; C_0402_1005Metric; Mfr. Part # GCM1555C1H201JA16D; LCSC # C710649
C1404: 10uF; C_0402_1005Metric; Mfr. Part # GRM155R61A106ME11D; LCSC # C408132
LS1401: CMS-160925-078L100-67; 16x9mm Speaker; Mfr. Part # CMS-160925-078L100-67; LCSC # C3311830
MK1401: SPH0645LM4H-B; Knowles_SPH0645LM4H-6_3.5x2.65mm; Mfr. Part # SPH0645LM4H-B; LCSC # NA
R1401, R1402, R1403: 47; R_0402_1005Metric; Mfr. Part # RC0402FR-0747RL; LCSC # C137973
R1404: 100K; R_0402_1005Metric; Mfr. Part # RC0402FR-07100KL; LCSC # C60491
R1405, R1406: 100K; R_0402_1005Metric; Mfr. Part # RC0402FR-07100KL; DigiKey # 311-100KLRCT-ND
U1401: MAX98357AETE_T; QFN50P300X300X80-17N; Mfr. Part # MAX98357AETE+T; LCSC # C910544

Connections:
+3V3: C1401.1, C1402.1, C1403.1, C1404.1, MK1401.5 (VDD), R1405.1, U1401.7 (VDD), U1401.8 (VDD__1)
GND: C1401.2, C1402.2, C1403.2, C1404.2, MK1401.2 (SEL), MK1401.3 (GND), R1404.1, R1406.2, U1401.3 (GND), U1401.11 (GND__1), U1401.15 (GND__2), U1401.17 (EP)
Mic_BCLK: MK1401.4 (BCLK), R1402.1, R1402.2
Mic_DATA: R1403.2
Mic_WS: MK1401.1 (WS), R1401.1, R1401.2
unnamed: LS1401.1, U1401.9 (OUTP)
unnamed: LS1401.2, U1401.10 (OUTN)
unnamed: MK1401.6 (DATA), R1403.1, R1404.2
unnamed: R1405.2, R1406.1, U1401.2 (GAIN_SLOT)
Speaker_BCLK: U1401.16 (BCLK)
Speaker_DIN: U1401.1 (DIN)
Speaker_LRCLK: U1401.14 (LRCLK)
Speaker_SD: U1401.4 (SD_MODE)

Notes on the sheet:
For simplicity's sake, both the microphone and speaker will be using the left channel modes. The left channel does not require any resistor on the speaker's SD_MODE pin, which is the only reason the left channel is preferential. [^4]
[^1] SPH0645LM4H-B.pdf (page 6) [^2] SPH0645LM4H-B.pdf (page 3) [^3] SPH0645LM4H-B.pdf (page 7) [^4] MAX98357A-MAX98357B.pdf (page 17) [^5] MAX98357A-MAX98357B.pdf (page 28)
R1401-R1403 are included to dampen or terminate their respective traces. If the traces are electrically long then they should be controlled impedance traces with impedance in the 50-120 Ohm range. Traces are considered electrically long when the length of the trace (in inches) is greater than 2 tim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
The Speaker amplifier is connected to the second of the I2S interfaces on the ESP32-S3 microcontroller. The exact pins will be decided during the process of laying out the PCB based on what is the most convenient.
The SELECT pin determines when the microphone drives the Data pin. When SELECT = LOW the DATA pin drives the SDIN bus when WS = LOW otherwise DATA = tri-state. When operating a single microphone on an I2S bus, a pull down resistor (100K Ohms) should be placed from the Data pin to ground to insure t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
The SPH0645LM4H microphone is a "bottom port" microphone, which means that it will have to be mounted on the underside of the PCB with a hole for the microphone's audio input port. The placement on the PCB will be influenced by the location of the Li-Po battery, which will be somewhat centrally loc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
The Microphone is connected to one of the two I2S interfaces on the ESP32-S3 microcontroller. The exact pins will be decided during the process of laying out the PCB based on what is most convenient.
Notes: [^1] 1. A decoupling capacitor (C1401) mounted as close as possible is required for optimum SNR. 2. An RF filter Capacitor (C1402) in the range of 20-200pF may be needed depending on the RF environment. 3. If both decoupling and RF filter capacitors are used, the RF filter capacitors should 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
Gain can be set by using different configurations connected to GAIN_SLOT. 15dB: if a 100K resistor is connected between GAIN_SLOT and GND 12dB: if GAIN_SLOT is connected directly to GND by bridging the R1406 footprint 9dB : if GAIN_SLOT is not connected to anything (this is the default) and no resi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
Speaker
Microphone
