Home-Sweet-Home-Assistant/Comms-Badge-Voice-Assistant/Hardware/KiCad Project/v0.1.1/Status_LED.kicad_sch

## KiCad design Hardware/KiCad Project/v0.1.1/Status_LED.kicad_sch (2024-03-10)

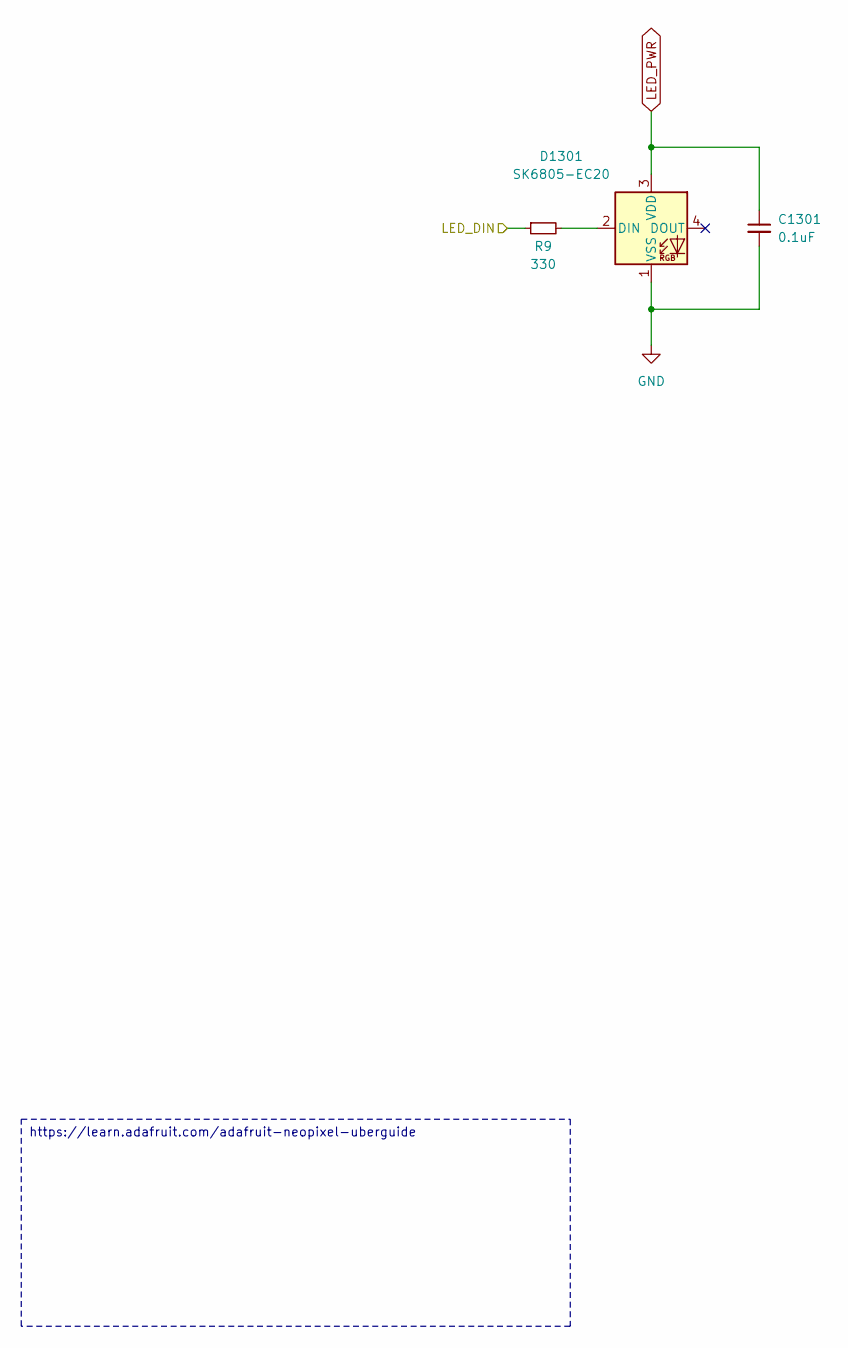
[picture p27: schematic Status_LED.kicad_sch]

Parts:
C1301: 0.1uF; C_0402_1005Metric; Mfr. Part # GRM155R61H104JE14D; LCSC # C426067
D1301: SK6805-EC20; LED_WS2812B-2020_PLCC4_2.0x2.0mm; Mfr. Part # SK6805-EC20; LCSC # C2890036
R9: 330; R_0402_1005Metric; Mfr. Part # RC0402FR-07330RL; LCSC # C105875

Connections:
GND: C1301.2, D1301.1 (VSS)
LED_DIN: R9.1
LED_PWR: C1301.1, D1301.3 (VDD)
unnamed: D1301.2 (DIN), R9.2

Notes on the sheet:
https://learn.adafruit.com/adafruit-neopixel-uberguide
