Home-Sweet-Home-Assistant/Comms-Badge-Voice-Assistant/Hardware/KiCad Project/v0.1.1/Touch_Sensor_Battery_Monitoring.kicad_sch

## KiCad design Hardware/KiCad Project/v0.1.1/Touch_Sensor_Battery_Monitoring.kicad_sch (2024-03-10)

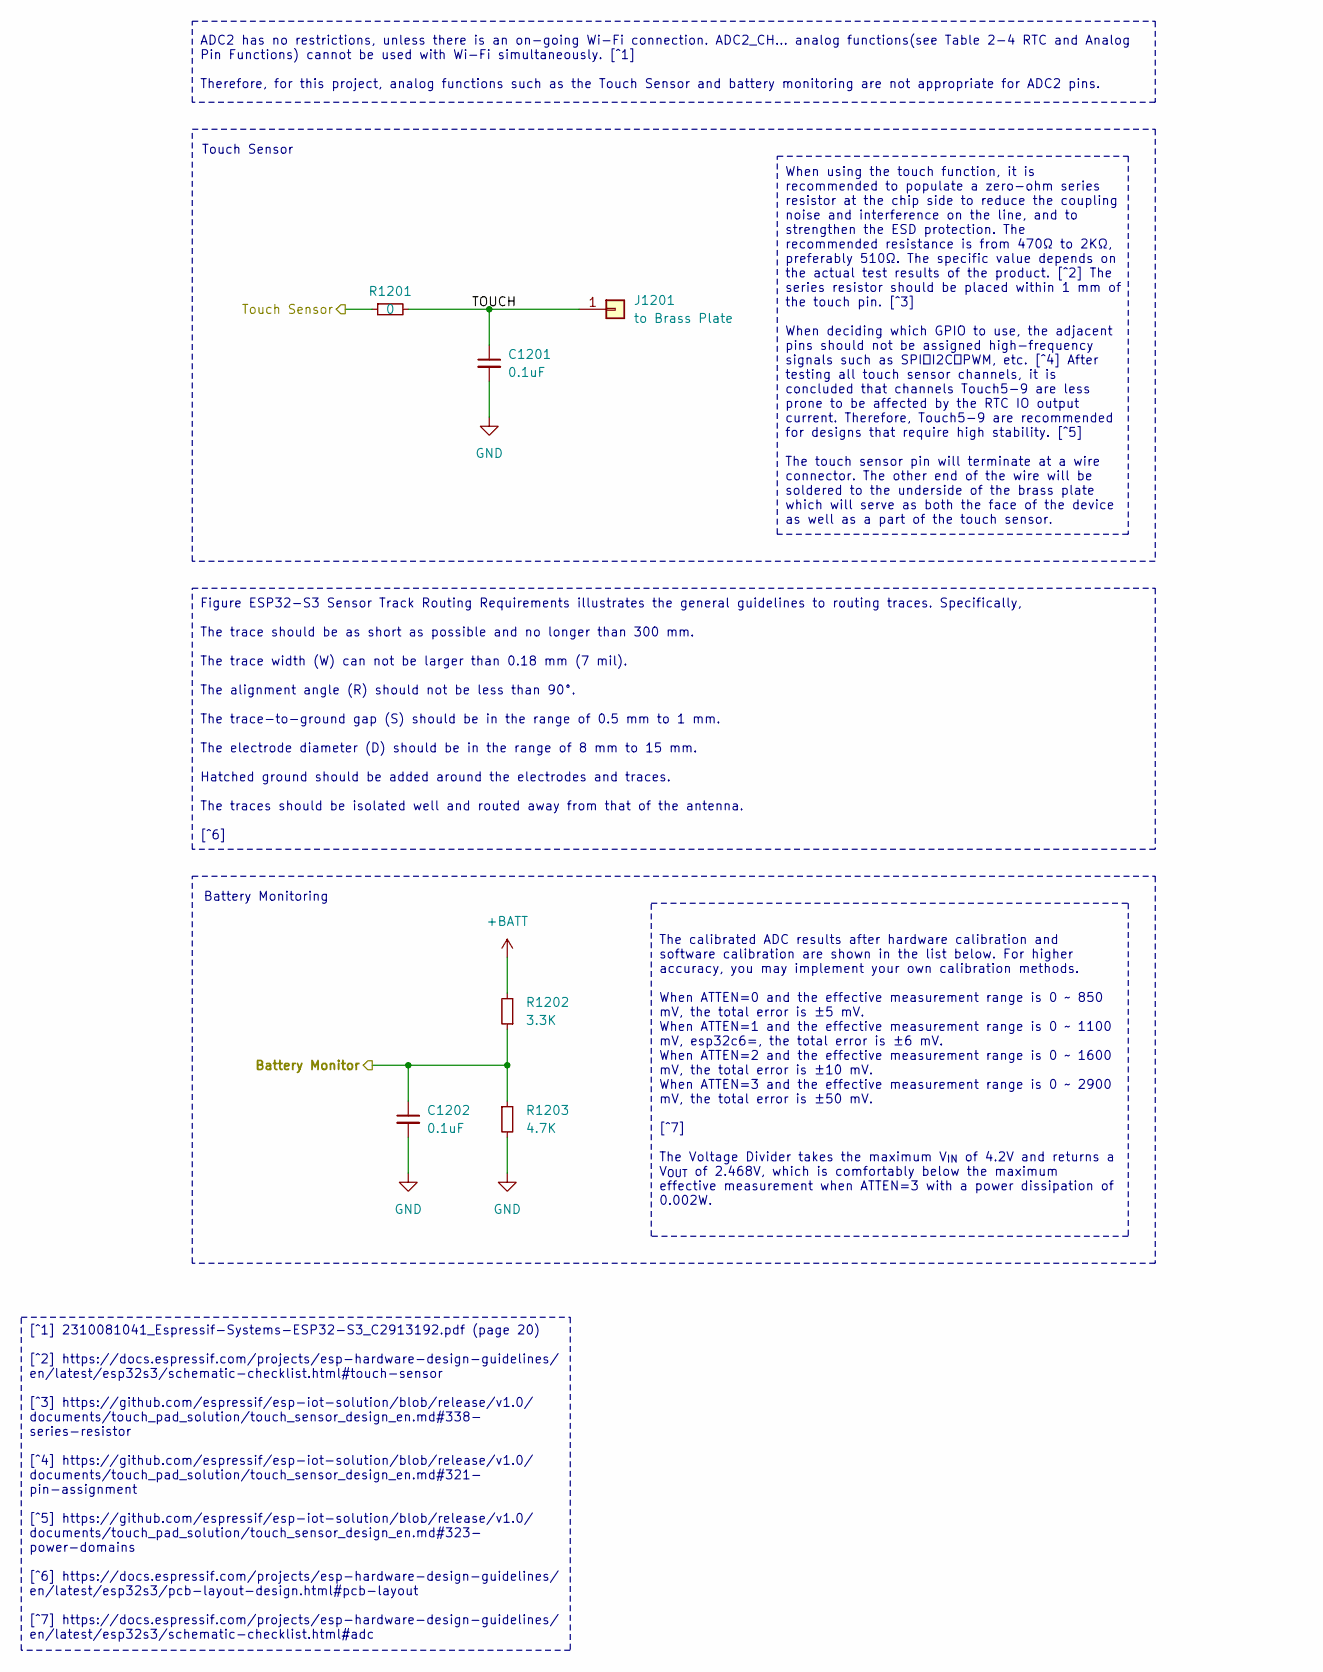
[picture p28: schematic Touch_Sensor_Battery_Monitoring.kicad_sch]

Parts:
C1201, C1202: 0.1uF; C_0402_1005Metric; Mfr. Part # GRM155R61H104JE14D; LCSC # C426067
J1201: to Brass Plate; SolderWire-0.5sqmm_1x01_D0.9mm_OD2.3mm
R1201: 0; R_0402_1005Metric; Mfr. Part # RC0402FR-070RL; LCSC # C106231
R1202: 3.3K; R_0402_1005Metric; Mfr. Part # RC0402FR-073K3L; DigiKey # 311-3.30KLRCT-ND
R1203: 4.7K; R_0402_1005Metric; Mfr. Part # RC0402FR-074K7L; DigiKey # 311-4.7KLRCT-ND

Connections:
+BATT: R1202.2
Battery Monitor: C1202.1, R1202.1, R1203.1
GND: C1201.2, C1202.2, R1203.2
TOUCH: C1201.1, J1201.1, R1201.2
Touch Sensor: R1201.1

Notes on the sheet:
Figure ESP32-S3 Sensor Track Routing Requirements illustrates the general guidelines to routing traces. Specifically, The trace should be as short as possible and no longer than 300 mm. The trace width (W) can not be larger than 0.18 mm (7 mil). The alignment angle (R) should not be less than 90°. 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
When using the touch function, it is recommended to populate a zero-ohm series resistor at the chip side to reduce the coupling noise and interference on the line, and to strengthen the ESD protection. The recommended resistance is from 470Ω to 2KΩ, preferably 510Ω. The specific value depends on th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
[^1] 2310081041_Espressif-Systems-ESP32-S3_C2913192.pdf (page 20) [^2] https://docs.espressif.com/projects/esp-hardware-design-guidelines/ en/latest/esp32s3/schematic-checklist.html#touch-sensor [^3] https://github.com/espressif/esp-iot-solution/blob/release/v1.0/ documents/touch_pad_solution/touch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
ADC2 has no restrictions, unless there is an on-going Wi-Fi connection. ADC2_CH… analog functions(see Table 2-4 RTC and Analog Pin Functions) cannot be used with Wi-Fi simultaneously. [^1] Therefore, for this project, analog functions such as the Touch Sensor and battery monitoring are not appropri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
The calibrated ADC results after hardware calibration and software calibration are shown in the list below. For higher accuracy, you may implement your own calibration methods. When ATTEN=0 and the effective measurement range is 0 ~ 850 mV, the total error is ±5 mV. When ATTEN=1 and the effective m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
Touch Sensor
Battery Monitoring
