Home-Sweet-Home-Assistant/Comms-Badge-Voice-Assistant/Hardware/KiCad Project/v0.1.1/USB-C_Port.kicad_sch

## KiCad design Hardware/KiCad Project/v0.1.1/USB-C_Port.kicad_sch (2024-03-10)

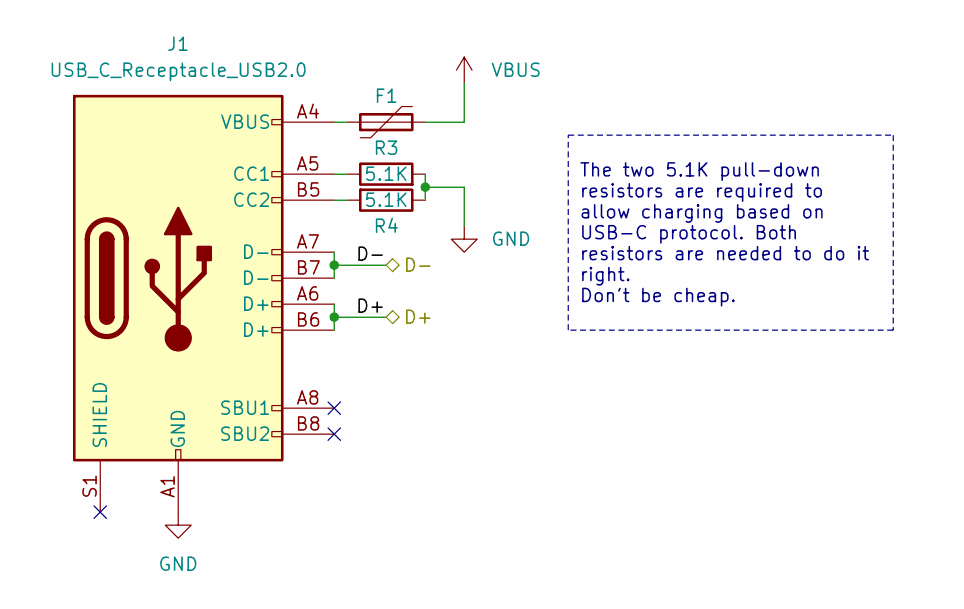
[picture p29: schematic USB-C_Port.kicad_sch]

Parts:
F1: Polyfuse; Fuse_0805_2012Metric_Pad1.15x1.40mm_HandSolder; Mfr. Part # 0805L200SL9AR; LCSC # C18198356
J1: USB_C_Receptacle_USB2.0; USB_C_Receptacle_GCT_USB4105-xx-A_16P_TopMnt_Horizontal; Mfr. Part # TYPE-C 16PIN 2MD(073); LCSC # C2765186
R3, R4: 5.1K; R_0402_1005Metric; Mfr. Part # RC0402FR-075K1L; LCSC # C105872

Connections:
D+: J1.A6 (D+), J1.B6 (D+)
D-: J1.A7 (D-), J1.B7 (D-)
GND: J1.A1 (GND), J1.A12 (GND), J1.B1 (GND), J1.B12 (GND), R3.2, R4.1
unnamed: F1.1, J1.A4 (VBUS), J1.A9 (VBUS), J1.B4 (VBUS), J1.B9 (VBUS)
unnamed: J1.A5 (CC1), R3.1
unnamed: J1.B5 (CC2), R4.2
VBUS: F1.2

Notes on the sheet:
The two 5.1K pull-down resistors are required to allow charging based on USB-C protocol. Both resistors are needed to do it right. Don't be cheap.
