Home-Sweet-Home-Assistant/Comms-Badge-Voice-Assistant/Hardware/KiCad Project/v0.1.1/USB_Data.kicad_sch

## KiCad design Hardware/KiCad Project/v0.1.1/USB_Data.kicad_sch (2024-03-10)

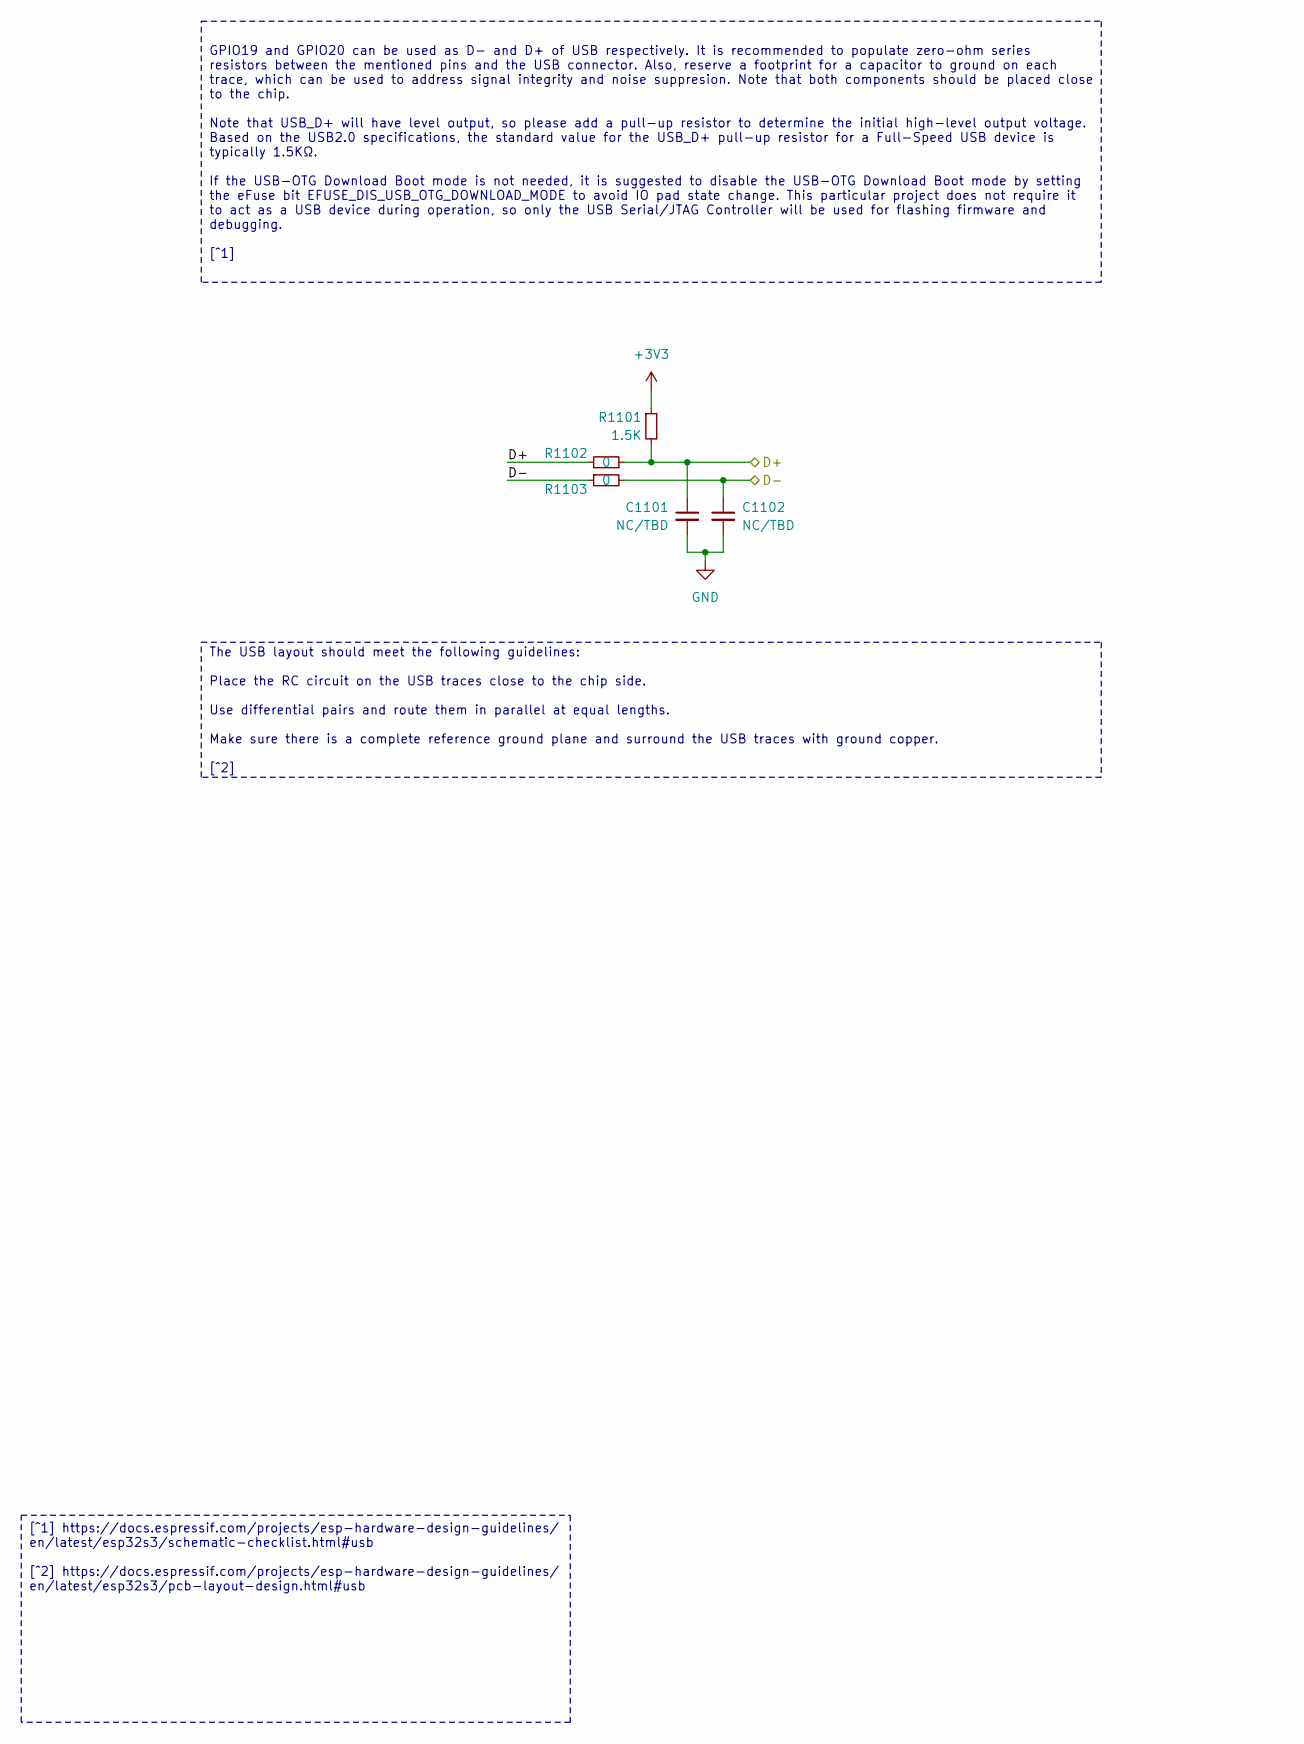
[picture p30: schematic USB_Data.kicad_sch]

Parts:
C1101, C1102: NC/TBD; C_0402_1005Metric
R1101: 1.5K; R_0402_1005Metric; Mfr. Part # RC0402FR-071K5L; LCSC # C114759
R1102, R1103: 0; R_0402_1005Metric; Mfr. Part # RC0402FR-070RL; LCSC # C106231

Connections:
+3V3: R1101.1
D+: C1101.1, R1101.2, R1102.1, R1102.2
D-: C1102.1, R1103.1, R1103.2
GND: C1101.2, C1102.2

Notes on the sheet:
[^1] https://docs.espressif.com/projects/esp-hardware-design-guidelines/ en/latest/esp32s3/schematic-checklist.html#usb [^2] https://docs.espressif.com/projects/esp-hardware-design-guidelines/ en/latest/esp32s3/pcb-layout-design.html#usb
The USB layout should meet the following guidelines: Place the RC circuit on the USB traces close to the chip side. Use differential pairs and route them in parallel at equal lengths. Make sure there is a complete reference ground plane and surround the USB traces with ground copper. [^2]
GPIO19 and GPIO20 can be used as D- and D+ of USB respectively. It is recommended to populate zero-ohm series resistors between the mentioned pins and the USB connector. Also, reserve a footprint for a capacitor to ground on each trace, which can be used to address signal integrity and noise suppre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
